MakeMagazinDE/Fledermaus-Scanner/Schaltplan KiCAD/Fledermaus.sch

## KiCad design Schaltplan KiCAD/Fledermaus.sch (2020-12-01)

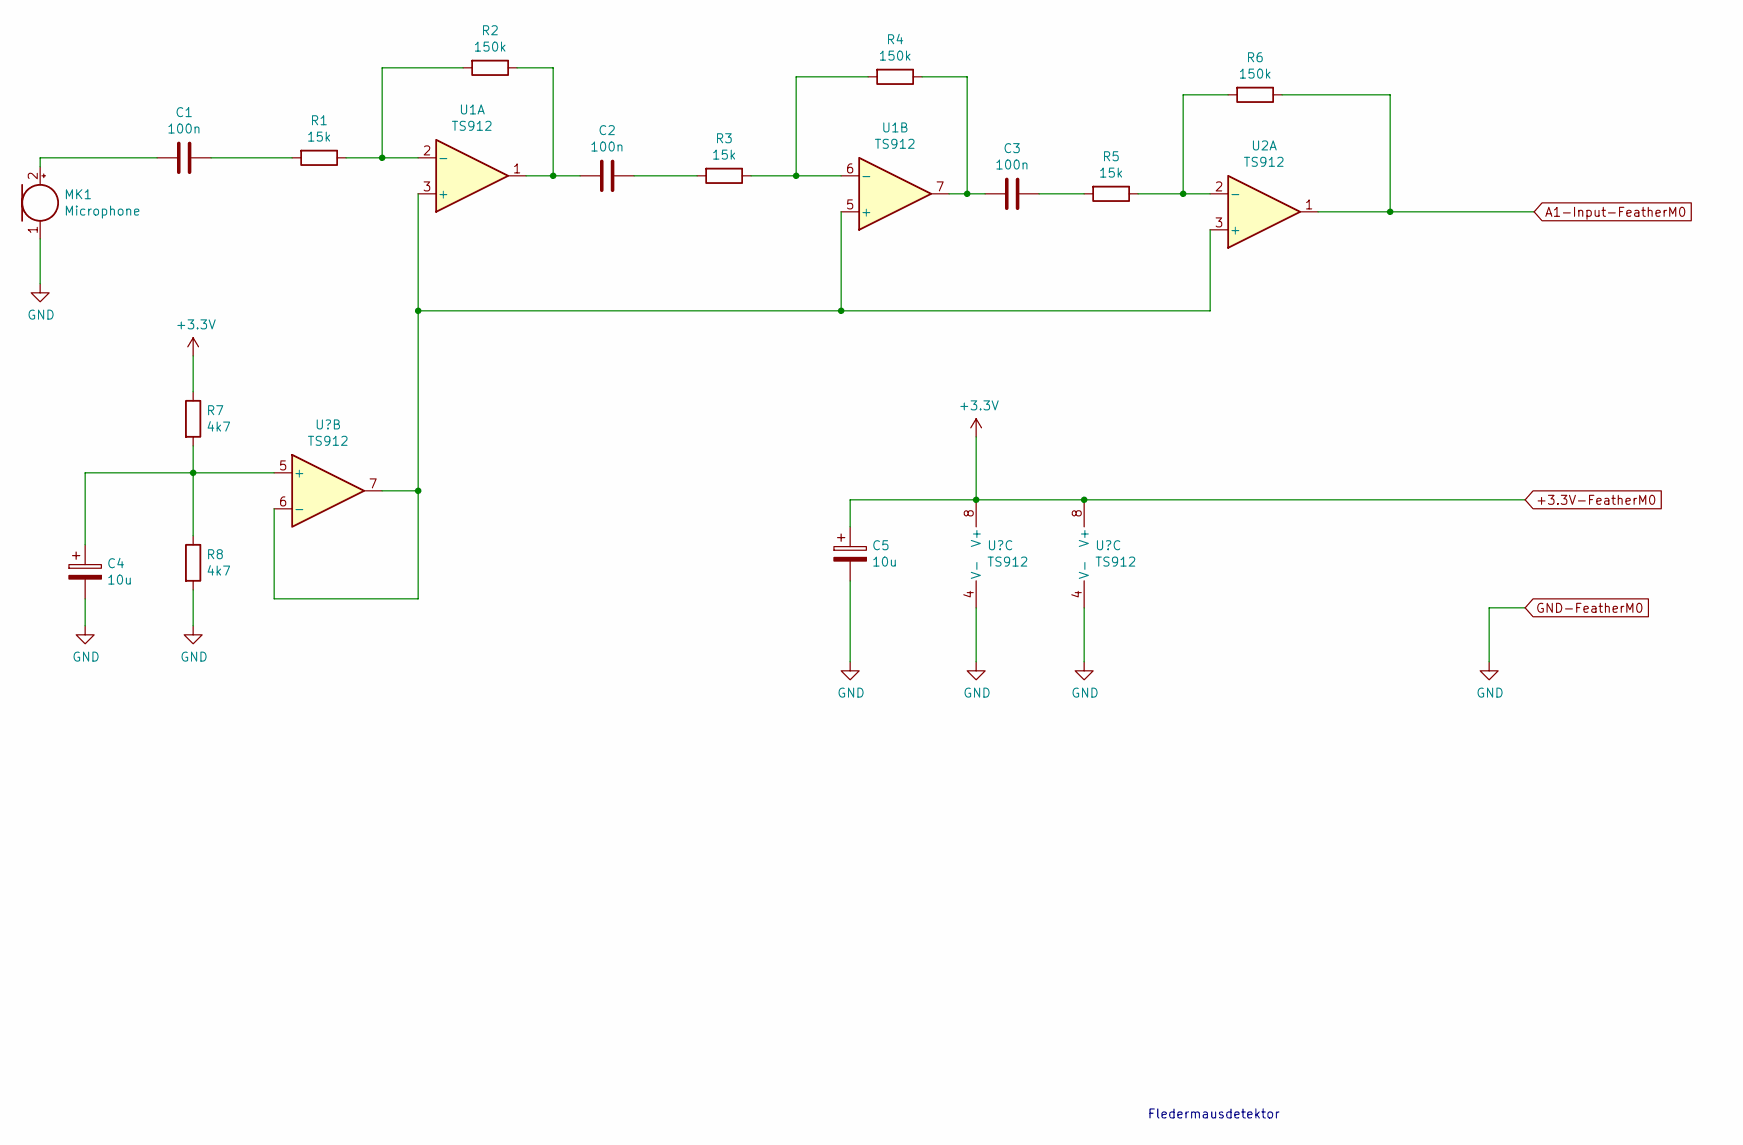
[picture p5: schematic Fledermaus.sch]

Parts:
C1, C2, C3: 100n
C4, C5: 10u
MK1: Microphone
R1, R3, R5: 15k
R2, R4, R6: 150k
R7, R8: 4k7
U1, U2: TS912

Connections:
+3.3V: C5.1, R7.1
A1-Input-FeatherM0: R6.1, U2.1
GND: C4.2, C5.2, MK1.1 (-), R8.2
unnamed: C1.1, R1.2
unnamed: C1.2, MK1.2 (+)
unnamed: C2.1, R3.2
unnamed: C2.2, R2.1, U1.1
unnamed: C3.1, R5.2
unnamed: C3.2, R4.1, U1.7
unnamed: C4.1, R7.2, R8.1
unnamed: R1.1, R2.2, U1.2 (-)
unnamed: R3.1, R4.2, U1.6 (-)
unnamed: R5.1, R6.2, U2.2 (-)
unnamed: U1.3 (+), U1.5 (+), U2.3 (+)

Notes on the sheet:
Fledermausdetektor
